sunng229/Micromouse/Inc/solver.h

#ifndef SOLVER_H
#define SOLVER_H

typedef enum Heading {NORTH, EAST, SOUTH, WEST} Heading;
typedef enum Action {LEFT, FORWARD, RIGHT, IDLE, TURNAROUND} Action;

Action solver();
Action leftWallFollower();
Action floodFill();

#endif
